adwjli/instrumentation-buoy-v1/main-board/raster/main-board-Back-bare.png

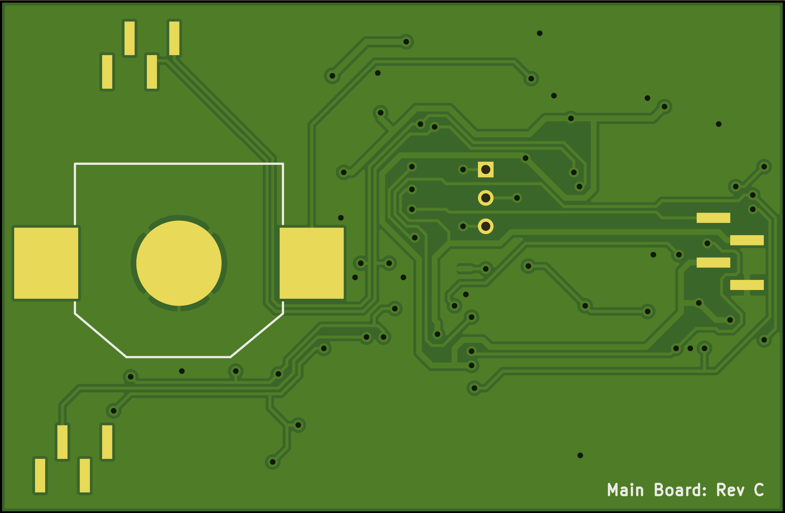
main-board/raster/main-board-Back-bare.png
