adwjli/instrumentation-buoy-v1/main-board/raster/main-board-Front-bare.png

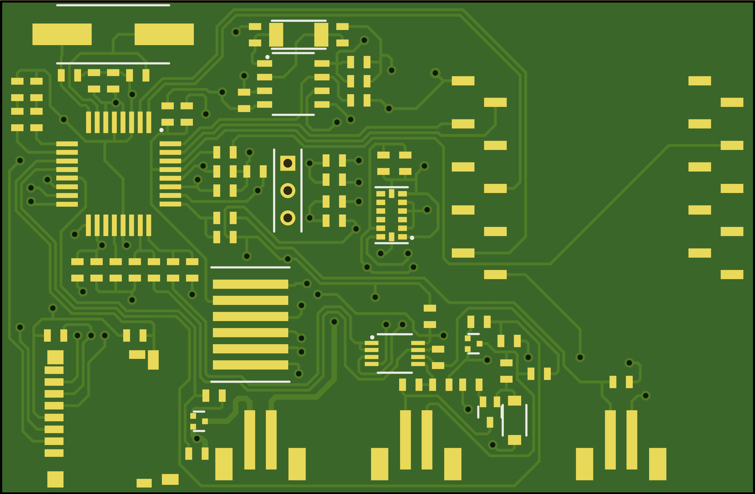
main-board/raster/main-board-Front-bare.png
