adwjli/instrumentation-buoy-v1/power-board/raster/power-board-Back-bare.png

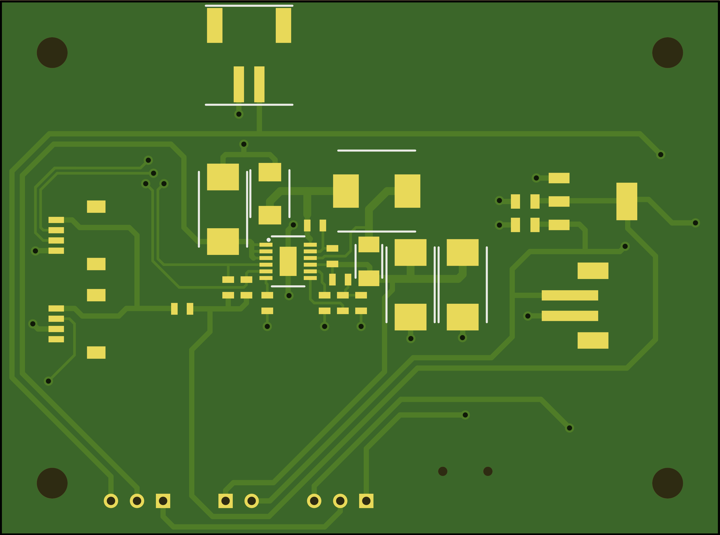
power-board/raster/power-board-Back-bare.png
