adwjli/instrumentation-buoy-v1/power-board/raster/power-board-Front-bare.png

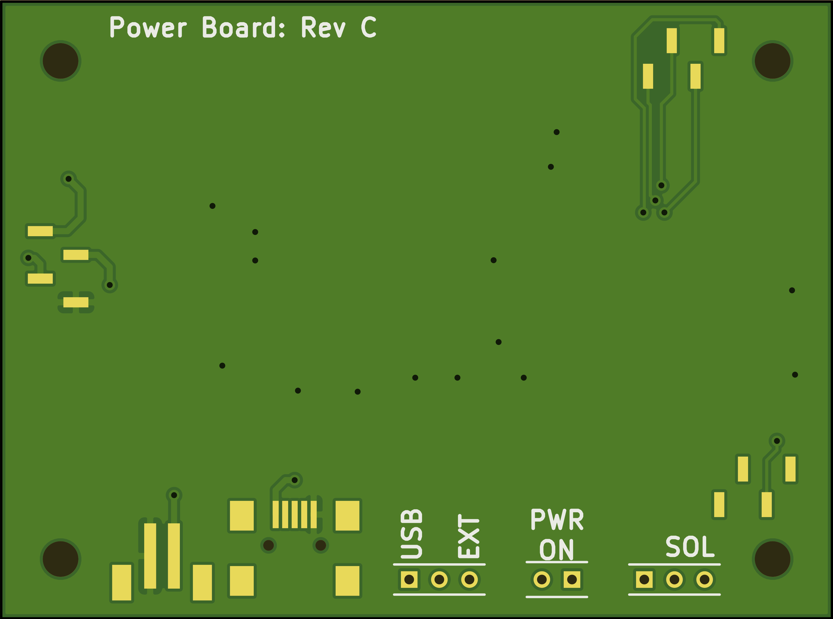
power-board/raster/power-board-Front-bare.png
